fabriziofiorucci/Streamdeck/images/3.jpg

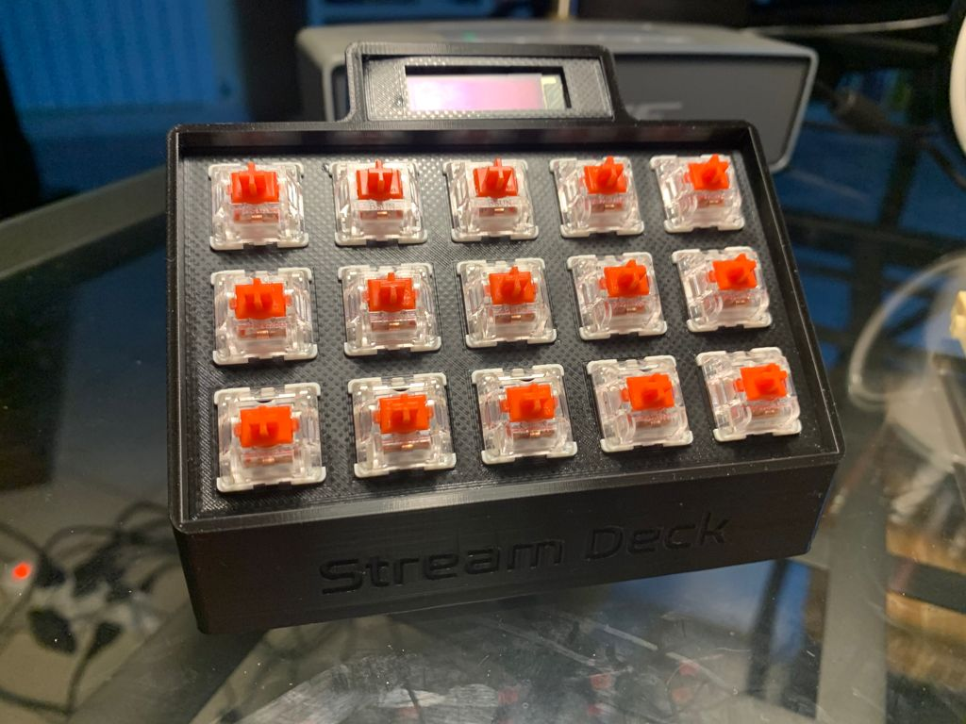
images/3.jpg
