fabriziofiorucci/Streamdeck/images/4.jpg

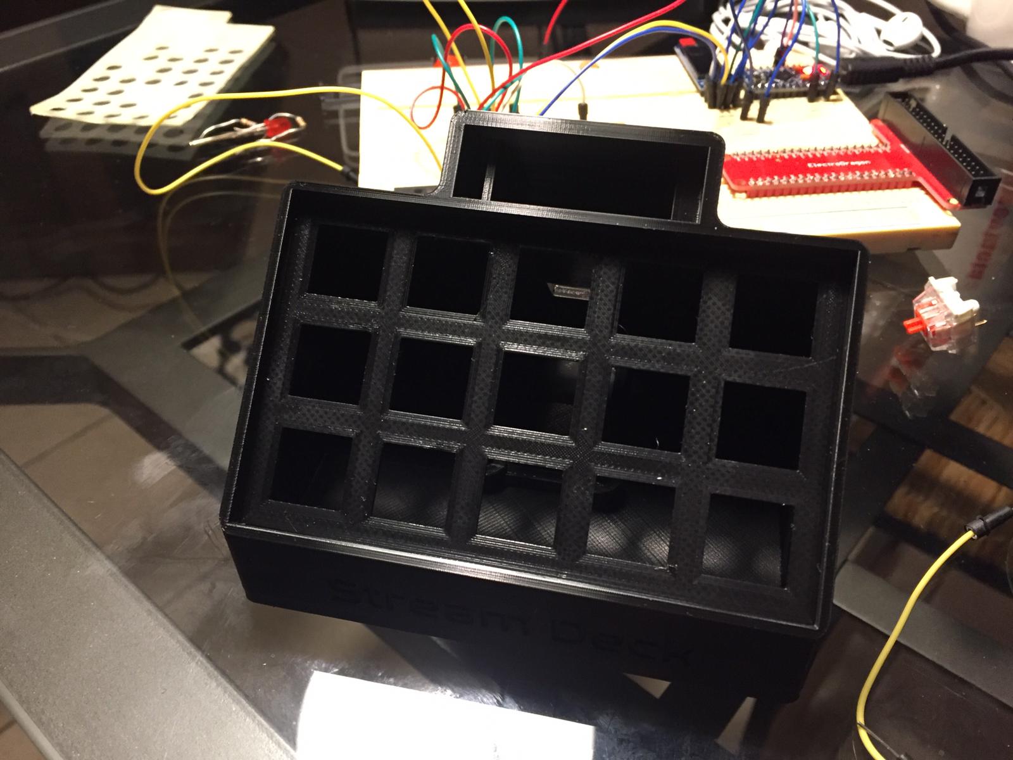
images/4.jpg
