fabriziofiorucci/Streamdeck/images/5.jpg

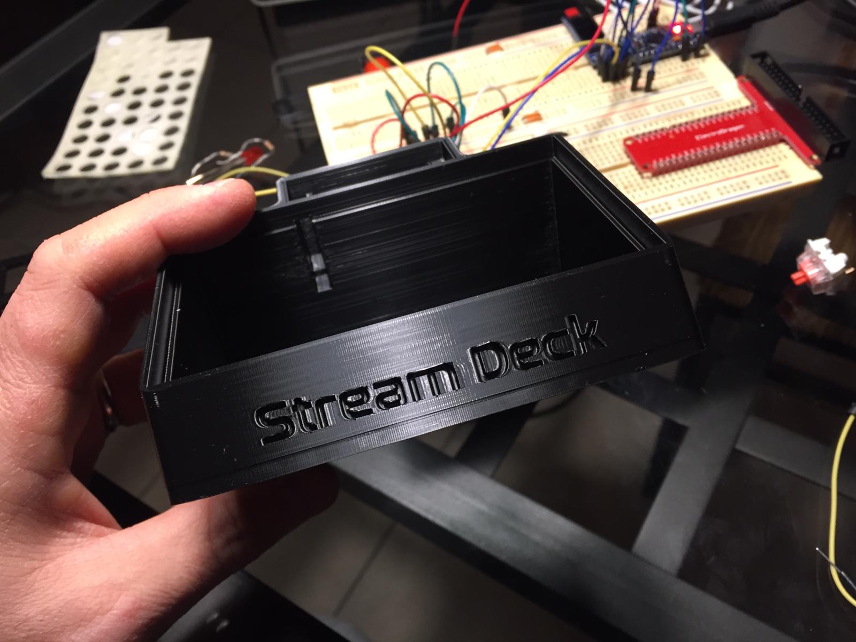
images/5.jpg
