fabriziofiorucci/Streamdeck/images/6.jpg

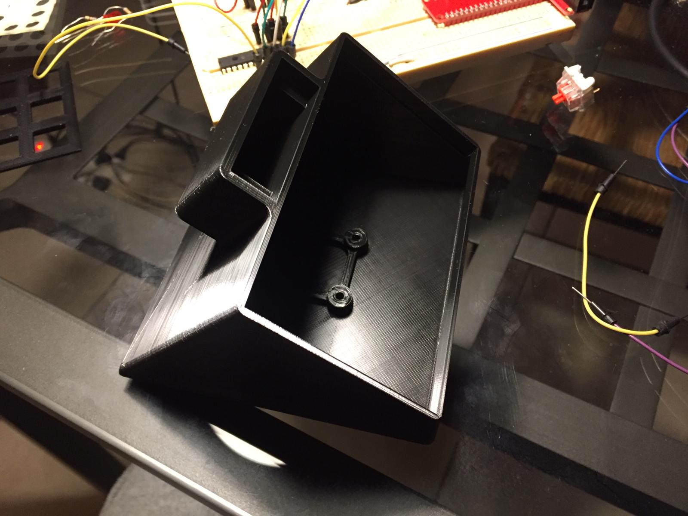
images/6.jpg
