fabriziofiorucci/Streamdeck/images/IMG_0749.JPG

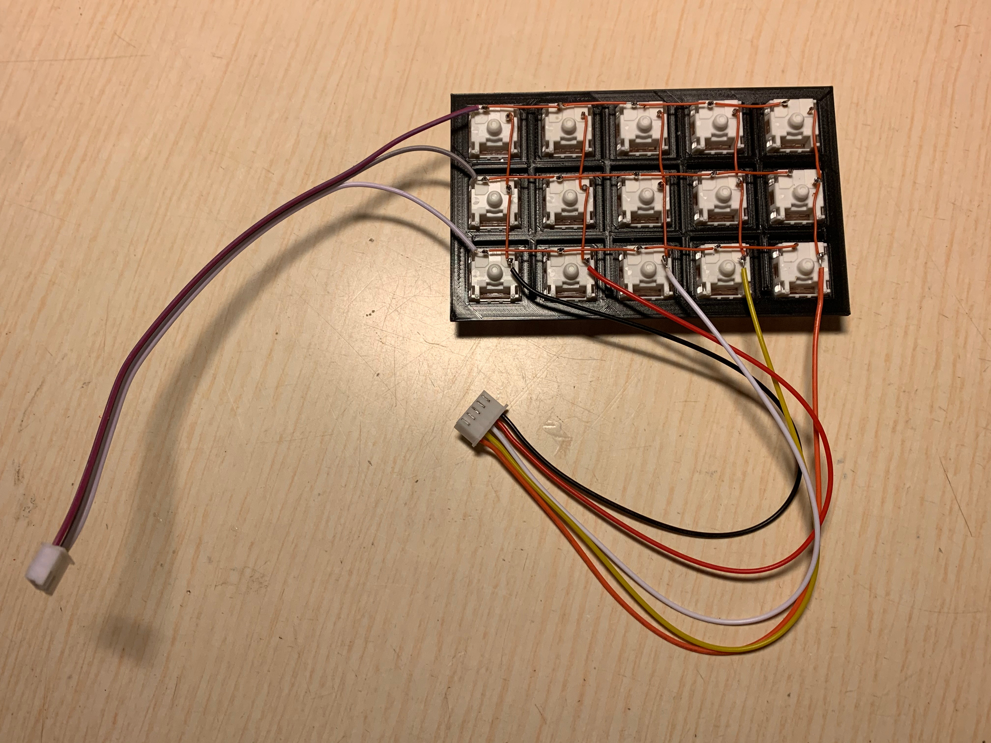
images/IMG_0749.JPG
