fabriziofiorucci/Streamdeck/images/IMG_0750.JPG

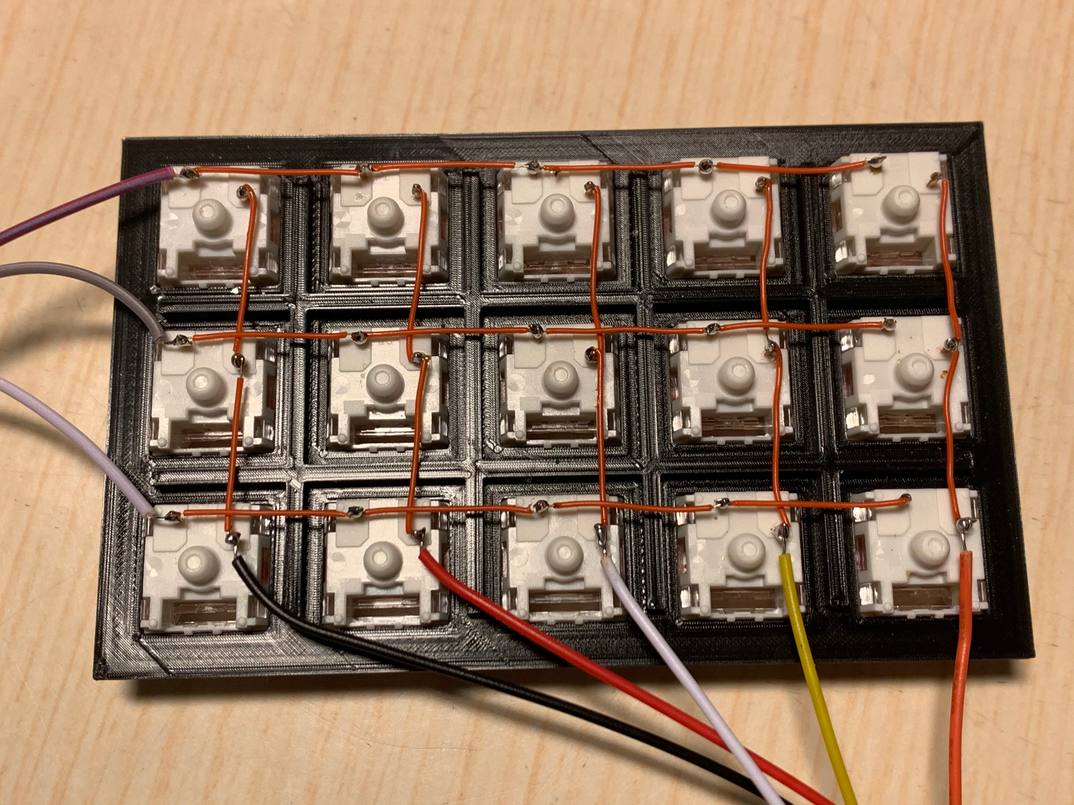
images/IMG_0750.JPG
