fabriziofiorucci/Streamdeck/images/IMG_0751.JPG

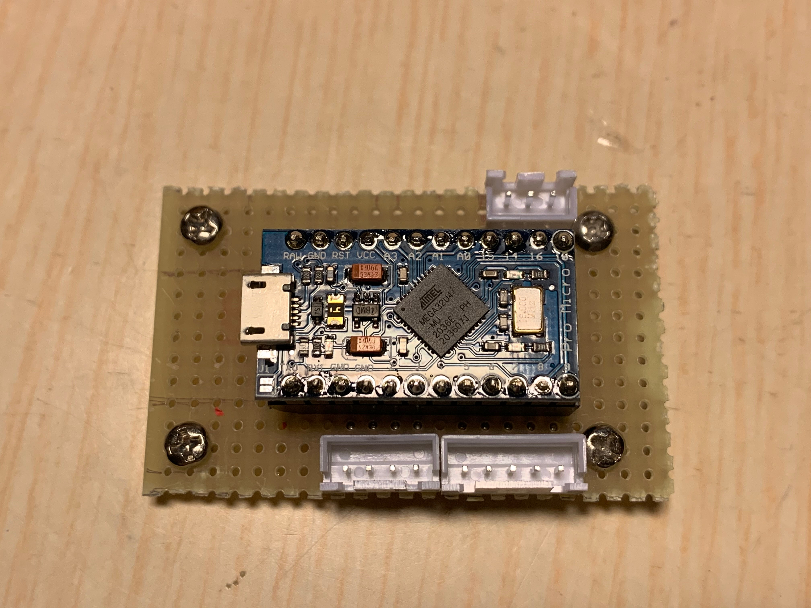
images/IMG_0751.JPG
