fabriziofiorucci/Streamdeck/images/IMG_0752.JPG

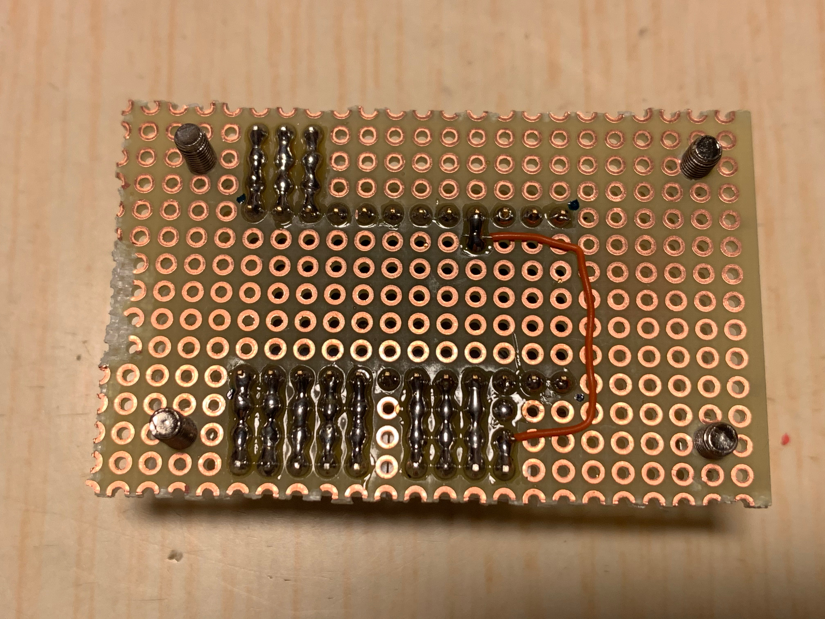
images/IMG_0752.JPG
