fabriziofiorucci/Streamdeck/images/IMG_0753.JPG

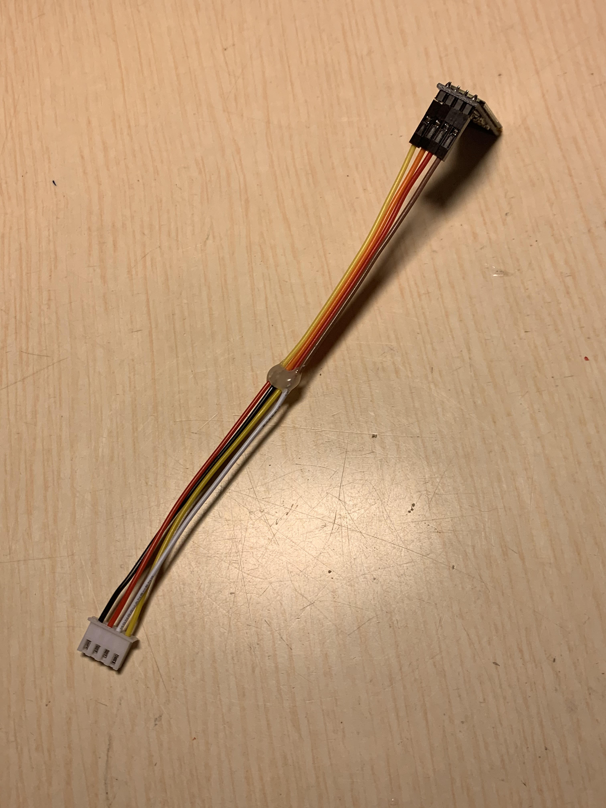
images/IMG_0753.JPG
