fabriziofiorucci/Streamdeck/images/IMG_0754.JPG

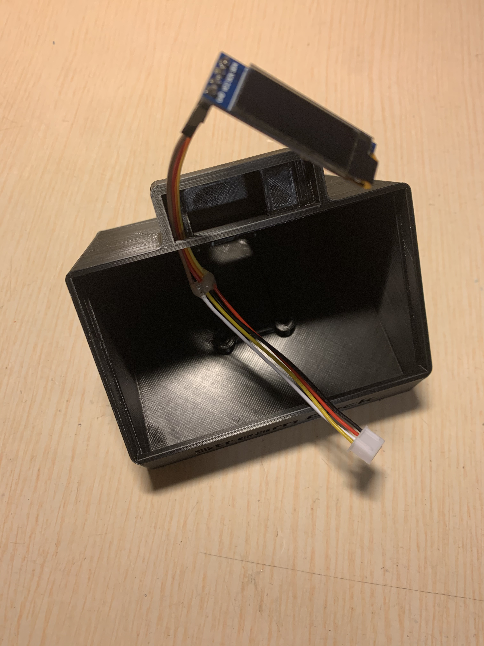
images/IMG_0754.JPG
