fabriziofiorucci/Streamdeck/images/IMG_0755.JPG

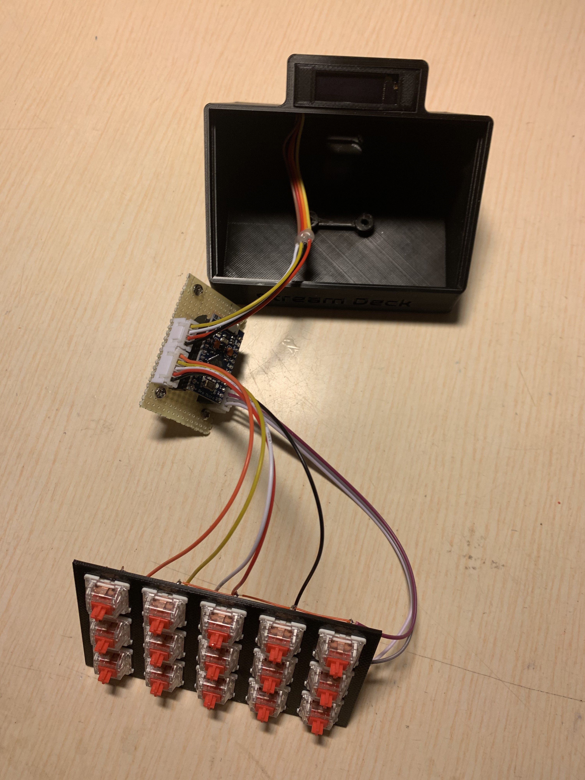
images/IMG_0755.JPG
