fabriziofiorucci/Streamdeck/images/IMG_0756.JPG

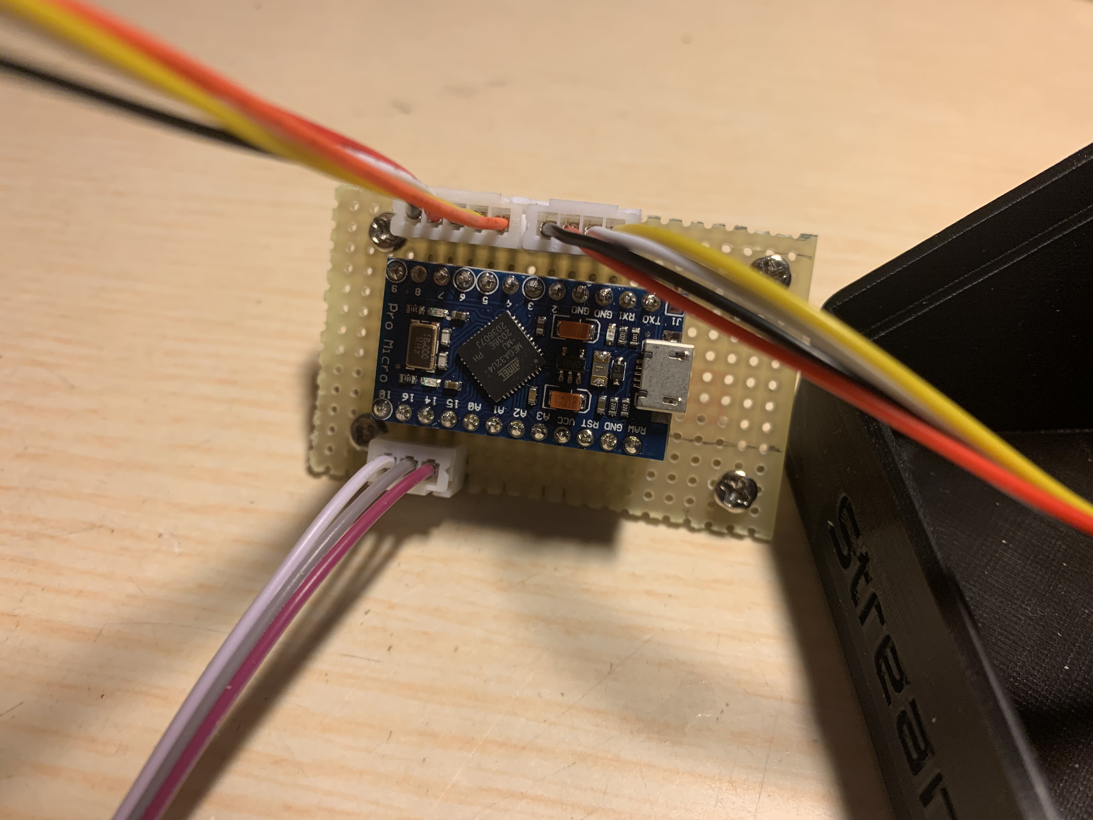
images/IMG_0756.JPG
